famichu/MagLevSwitch_ReferenceKeyboard/src/Arduino/MaglevSwitch_Board.h

#include <stdio.h>
#include "pico/stdlib.h"
#include "hardware/adc.h"
#include "hardware/gpio.h"
#include "hardware/i2c.h"
#include "hardware/flash.h"
#include "hardware/sync.h"
#include "typedef_common.h"
#include "typedef_v0.h"
#include "typedef_v1.h"
#include "Threshold_Data.h"

#ifndef MAGLEV_SWITCH_BOARD
#define MAGLEV_SWITCH_BOARD

const int MLSW_LOWER_LIMIT  = 1070;
const int MLSW_UPPER_LIMIT  = 3170;
const int MLSW_RANGE        = MLSW_UPPER_LIMIT - MLSW_LOWER_LIMIT;

static const unsigned char LOGO[] = { // Logo img
  0xff, 0xff, 0xff, 0xff, 0xff, 0xff, 0xff, 0xff, 0xff, 0xff, 0xff, 0xff, 0xff, 0xff, 0xff, 0xff, 
  0xff, 0xef, 0xdf, 0xff, 0xff, 0xf7, 0xff, 0xff, 0xff, 0xc3, 0xff, 0xbf, 0xff, 0xdf, 0xff, 0xff, 
  0xff, 0xcf, 0xcf, 0xff, 0xff, 0xf7, 0xff, 0xff, 0xff, 0xbd, 0xff, 0xff, 0xfd, 0xdf, 0xff, 0xff, 
  0xff, 0xcf, 0xc7, 0xff, 0xff, 0xf7, 0xff, 0xff, 0xff, 0xfe, 0xff, 0xff, 0xfd, 0xdf, 0xff, 0xff, 
  0xff, 0xaf, 0xd7, 0xa1, 0x47, 0xf7, 0x0f, 0xee, 0xfd, 0xfe, 0xdd, 0x9b, 0x60, 0x50, 0xf8, 0xff, 
  0xff, 0xaf, 0xdb, 0x9e, 0x3b, 0xf7, 0xf7, 0xed, 0xfd, 0xfd, 0xdd, 0xbb, 0xbd, 0x9f, 0xf7, 0xff, 
  0xff, 0x6f, 0x5b, 0xbf, 0x7d, 0xf7, 0xf7, 0xed, 0xfd, 0xe3, 0x9d, 0xbb, 0xbd, 0xdf, 0xf7, 0xff, 
  0xff, 0x6f, 0x5d, 0xbf, 0x7d, 0xf7, 0xf7, 0xdd, 0xfe, 0xdf, 0x5b, 0xbd, 0xbd, 0xdf, 0xf7, 0xff, 
  0xff, 0xef, 0x5c, 0xbf, 0x7d, 0xf7, 0x07, 0xdc, 0xfe, 0xbf, 0x6b, 0xbd, 0xbd, 0xdf, 0xf7, 0xff, 
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
    uint8_t outCodesCnt_;
    bool encoderSwPressed_;
    
    int8_t fnSw_;

    ThresholdData* actuationDepth_;
    ThresholdData* releaseDepth_;
    uint16_t currentDepth_[4];
    uint16_t prevDepth_[4];
    bool rangePrev_[4];
    bool isGoingDownPrev_[4];
    bool pressedPrev_[4];

    bool (MaglevSwitchBoard::*updateFunc)(void);

    void updateEncoderSwitch(void);
    void updateAnalogueSwitch(void);
    void updateDigitalSwitch(void);
    void updateMatrix(void);

    void makeSendCodes(void);
    void switchLayer(void);
    
    uint8_t countSetBits(uint32_t n);
    void getActiveCodes(uint32_t bits, uint8_t distNum);

    bool isPressed(uint8_t idx);
    bool isNegative(uint16_t minuend,uint16_t subtrahend);
    bool getDirection(uint16_t prev, uint16_t current);
    uint8_t getTurning(bool direction, bool directionPrev, uint8_t modePrev);
    bool getStaying(uint16_t prev, uint16_t current, uint8_t range, uint8_t rangePrev);
    uint8_t getRange(uint16_t current, uint16_t release_, uint16_t actuation);
};
#endif
