famichu/MagLevSwitch_ReferenceKeyboard/src/Arduino/typedef_common.h

#ifndef TYPEDEF_COMMON_H
#define TYPEDEF_COMMON_H

const uint8_t SW_NUM_DEFAULT          = 0;
const uint8_t DIRECT_SW_NUM_DEFAULT   = 0;
const uint8_t MATRIX_OUT_NUM_DEFAULT  = 0;
const uint8_t MATRIX_IN_NUM_DEFAULT   = 0;
const uint8_t SW_GPIO_DEFAULT         = 0;
const uint8_t MATRIX_OUT_GPIO_DEFAULT = 0;
const uint8_t MATRIX_IN_GPIO_DEFAULT  = 0;

const char FN = 0x00;
const uint8_t MLSW_NUM = 4;

const uint32_t STATUS_BIT_SW1   = 0b0000000000000000000000000001;
const uint32_t STATUS_BIT_SW2   = 0b0000000000000000000000000010;
const uint32_t STATUS_BIT_SW3   = 0b0000000000000000000000000100;
const uint32_t STATUS_BIT_SW4   = 0b0000000000000000000000001000;
const uint32_t STATUS_BIT_SW5   = 0b0000000000000000000000010000;
const uint32_t STATUS_BIT_SW6   = 0b0000000000000000000000100000;
const uint32_t STATUS_BIT_SW7   = 0b0000000000000000000001000000;
const uint32_t STATUS_BIT_SW8   = 0b0000000000000000000010000000;
const uint32_t STATUS_BIT_MLSW1 = 0b0000000000000000000100000000;
const uint32_t STATUS_BIT_SW9   = 0b0000000000000000001000000000;
const uint32_t STATUS_BIT_SW10  = 0b0000000000000000010000000000;
const uint32_t STATUS_BIT_SW11  = 0b0000000000000000100000000000;
const uint32_t STATUS_BIT_SW12  = 0b0000000000000001000000000000;
const uint32_t STATUS_BIT_MLSW2 = 0b0000000000000010000000000000;
const uint32_t STATUS_BIT_MLSW3 = 0b0000000000000100000000000000;
const uint32_t STATUS_BIT_MLSW4 = 0b0000000000001000000000000000;
const uint32_t STATUS_BIT_SW13  = 0b0000000000010000000000000000;
const uint32_t STATUS_BIT_SW14  = 0b0000000000100000000000000000;
const uint32_t STATUS_BIT_SW15  = 0b0000000001000000000000000000;
const uint32_t STATUS_BIT_SW16  = 0b0000000010000000000000000000;
const uint32_t STATUS_BIT_SW17  = 0b0000000100000000000000000000;
const uint32_t STATUS_BIT_SW18  = 0b0000001000000000000000000000;
const uint32_t STATUS_BIT_SW19  = 0b0000010000000000000000000000;
const uint32_t STATUS_BIT_SW20  = 0b0000100000000000000000000000;
const uint32_t STATUS_BIT_SW21  = 0b0001000000000000000000000000;
const uint32_t STATUS_BIT_SW22  = 0b0010000000000000000000000000;
const uint32_t STATUS_BIT_SW23  = 0b0100000000000000000000000000;
const uint32_t STATUS_BIT_SW24  = 0b1000000000000000000000000000;

const uint8_t MLSW_GPIO[] = {
  26, 
  29, 28, 27
};

const uint8_t ADC_NUM[] = {
  0, 
  3, 2, 1
};

const uint32_t STATUS_BITS_MLSW[] = {
    STATUS_BIT_MLSW1, 
    STATUS_BIT_MLSW2, 
    STATUS_BIT_MLSW3, 
    STATUS_BIT_MLSW4
};

const uint8_t ENCODER_A   = 12;
const uint8_t ENCODER_B   = 14;
const uint8_t ENCODER_SW  = 13;

#endif
